OpenSourceProtogenCollection/flexOS/logistics/fullsuit-diagram-blank.jpg

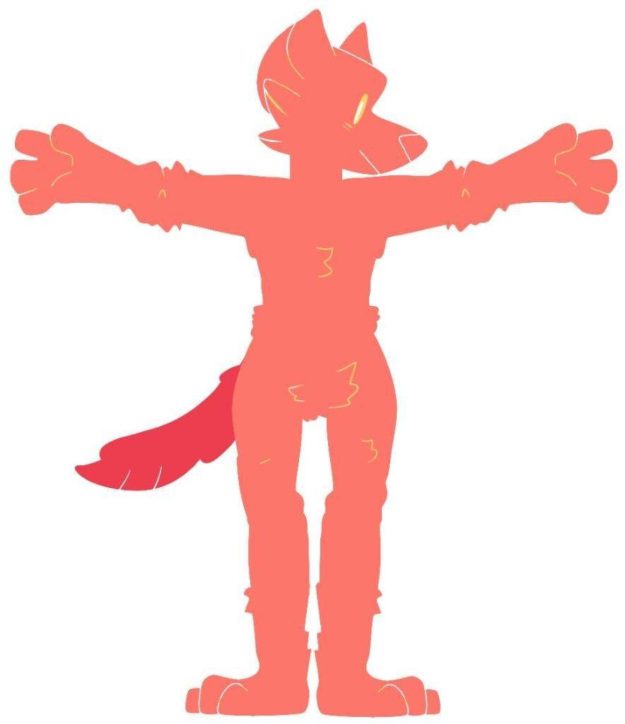
logistics/fullsuit-diagram-blank.jpg
