OpenSourceProtogenCollection/flexOS/logistics/fullsuit-diagram.jpg

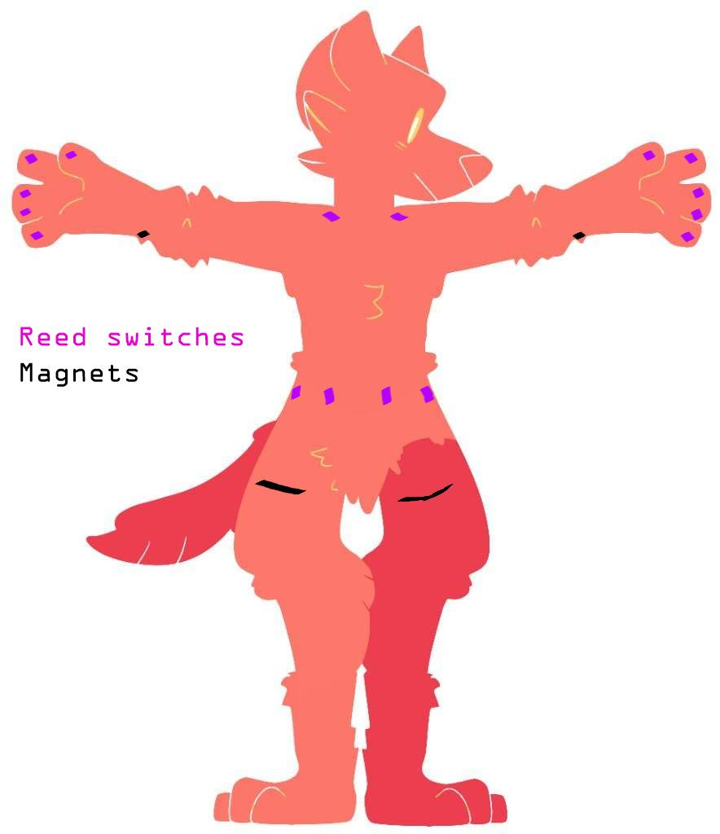
logistics/fullsuit-diagram.jpg
