OpenSourceProtogenCollection/flexOS/matrix-design/design-prototypes/charging/mouth/pixil-gif-drawing-black.gif

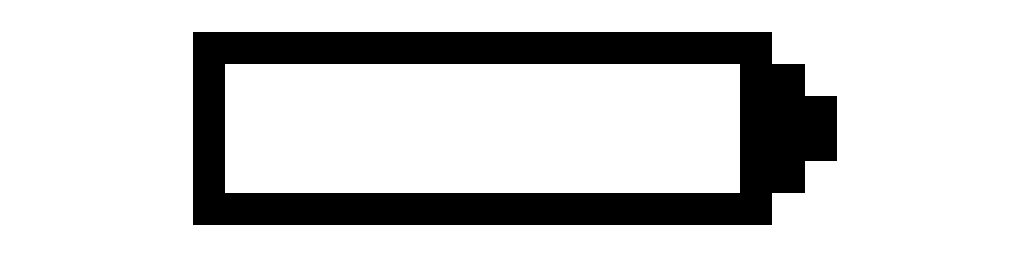
matrix-design/design-prototypes/charging/mouth/pixil-gif-drawing-black.gif
