OpenSourceProtogenCollection/flexOS/matrix-design/design-prototypes/error/pixil-gif-drawing (1).gif

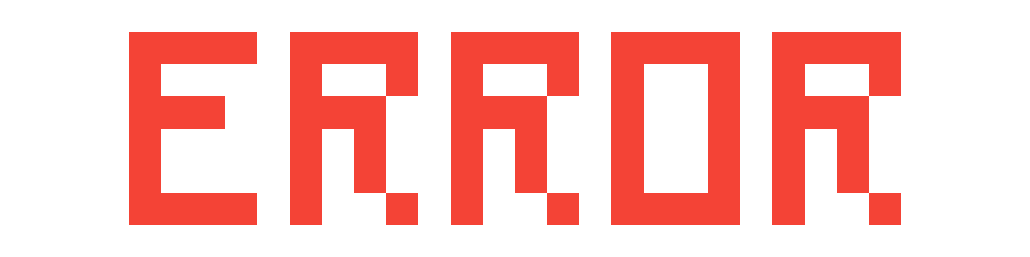
matrix-design/design-prototypes/error/pixil-gif-drawing (1).gif
