OpenSourceProtogenCollection/flexOS/matrix-design/design-prototypes/eyes-id/pixil-gif-drawing.gif

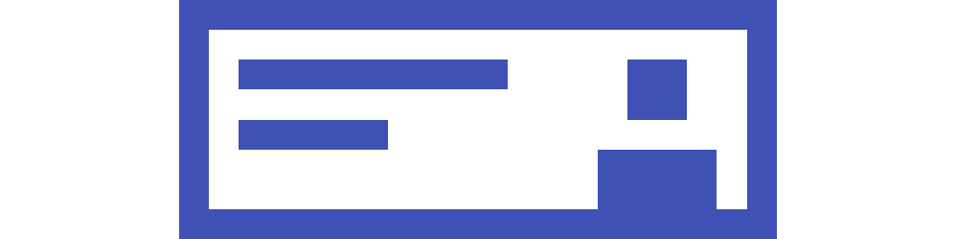
matrix-design/design-prototypes/eyes-id/pixil-gif-drawing.gif
