OpenSourceProtogenCollection/flexOS/matrix-design/design-prototypes/legs/pixil-gif-drawing (1).gif

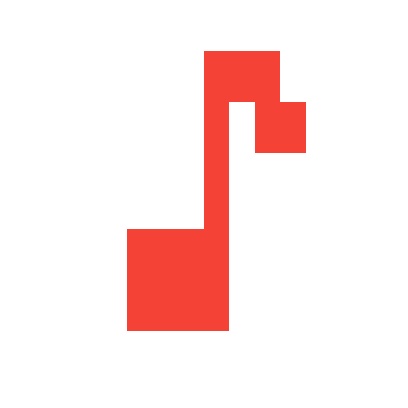
matrix-design/design-prototypes/legs/pixil-gif-drawing (1).gif
