OpenSourceProtogenCollection/flexOS/matrix-design/design-prototypes/low-battery/mouth/pixil-gif-drawing.gif

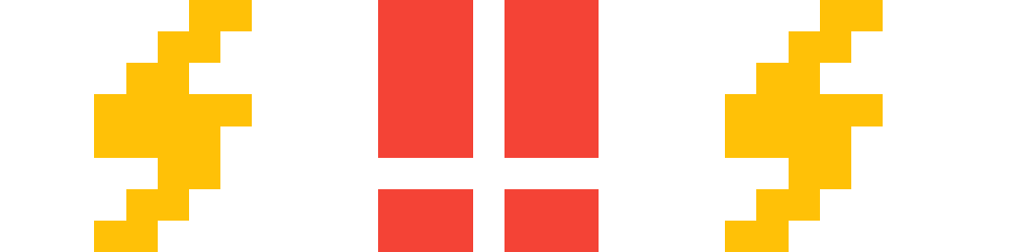
matrix-design/design-prototypes/low-battery/mouth/pixil-gif-drawing.gif
