OpenSourceProtogenCollection/flexOS/matrix-design/grid-16x16.png

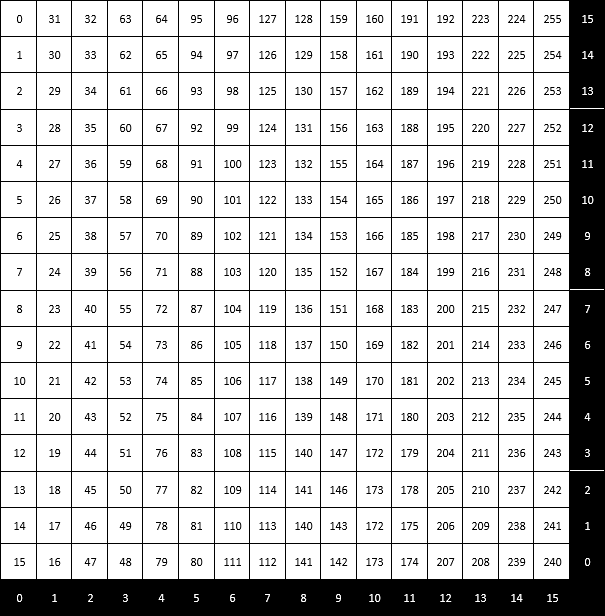
matrix-design/grid-16x16.png
