OpenSourceProtogenCollection/flexOS/matrix-design/grid-32x8.png

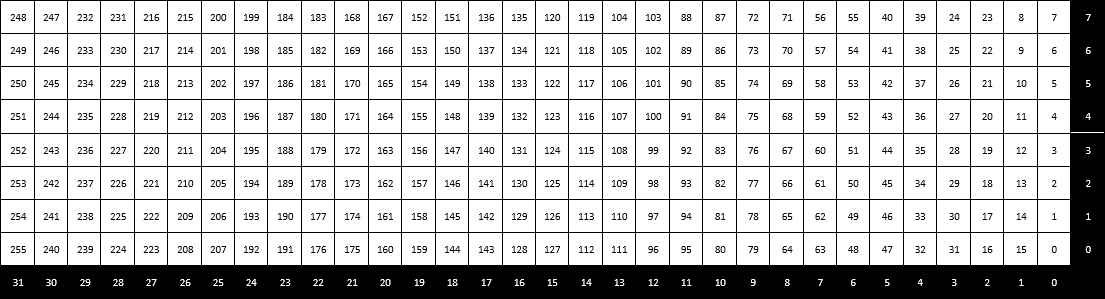
matrix-design/grid-32x8.png
