OpenSourceProtogenCollection/flexOS/modeling/armour_2.jpg

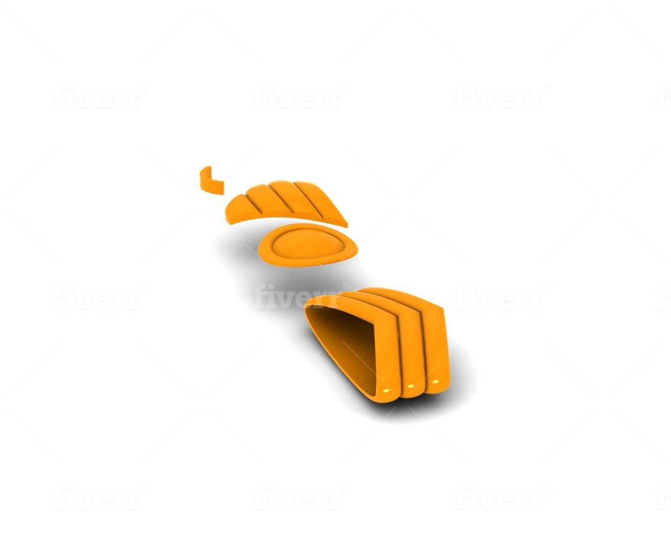
modeling/armour_2.jpg
