OpenSourceProtogenCollection/flexOS/logistics/full-setup.png

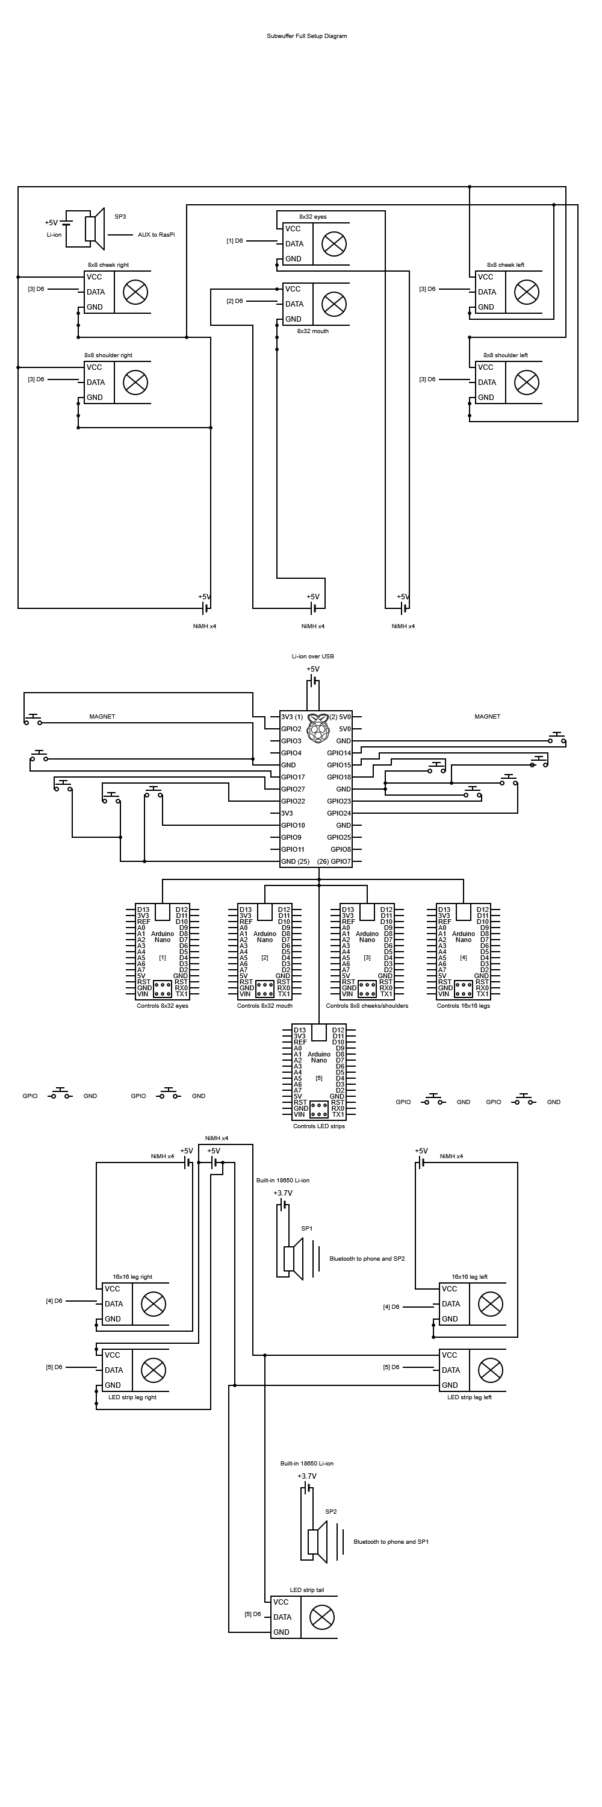
logistics/full-setup.png
