OpenSourceProtogenCollection/flexOS/modeling/commission.png

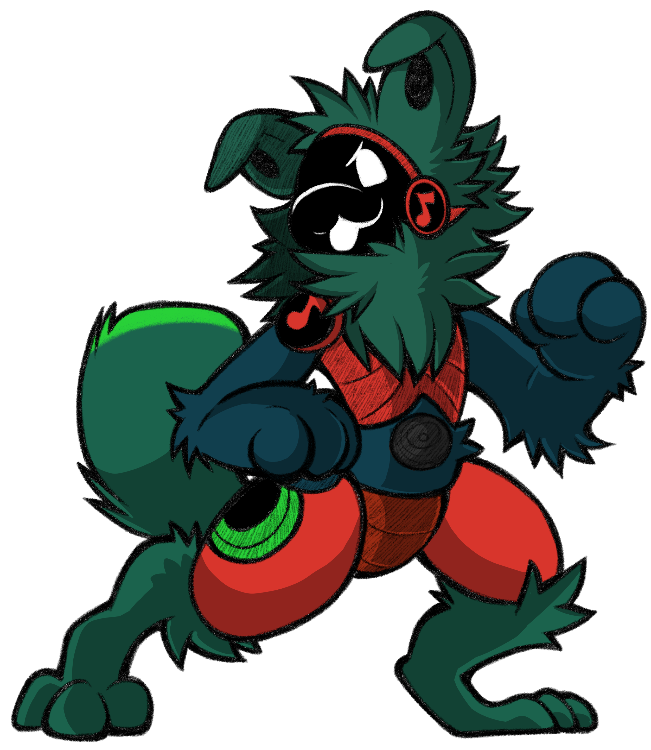
modeling/commission.png
